Megazoids-Hut/PicoPocket/images/1.jpg

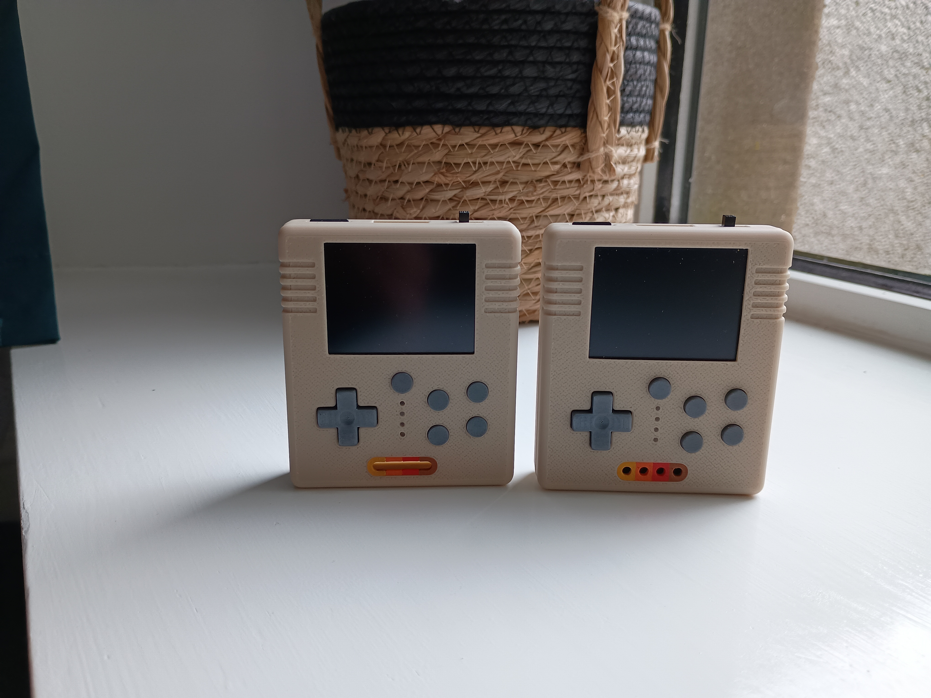
images/1.jpg
