Megazoids-Hut/PicoPocket/images/2.jpg

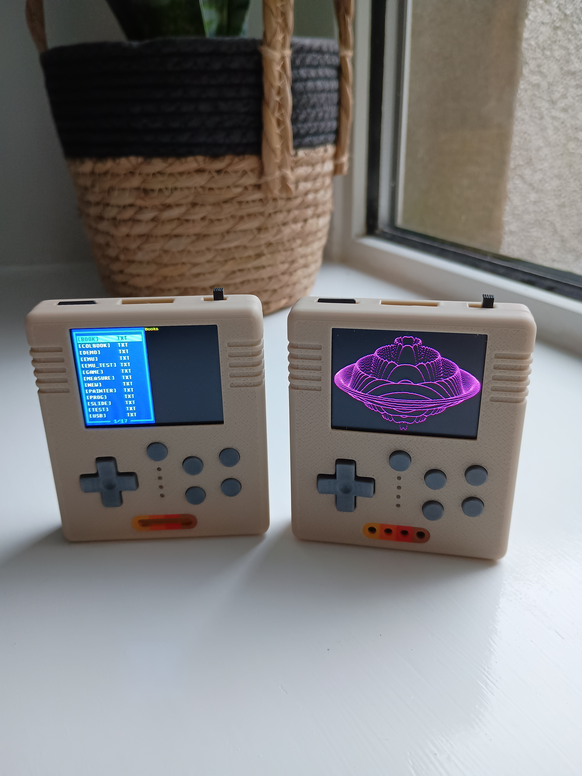
images/2.jpg
