Megazoids-Hut/PicoPocket/images/3.jpg

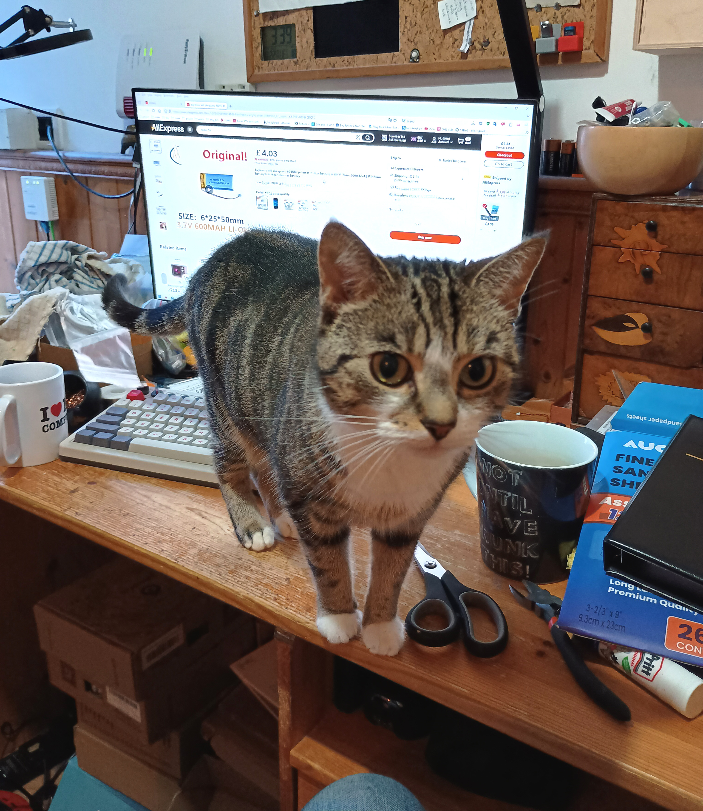
images/3.jpg
