Megazoids-Hut/PicoPocket/images/4.jpg

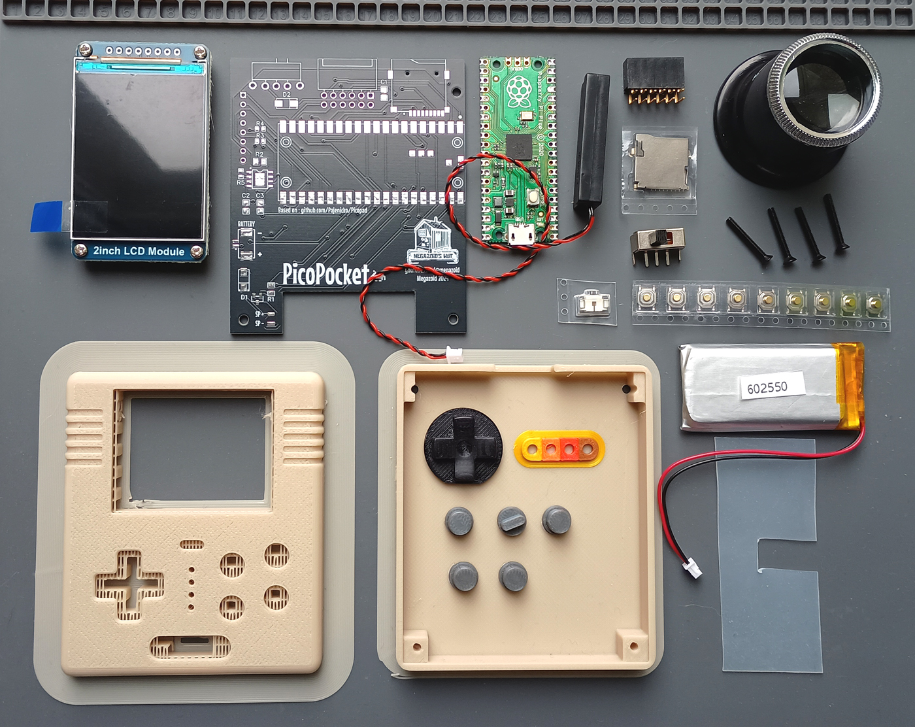
images/4.jpg
