Megazoids-Hut/PicoPocket/images/5.jpg

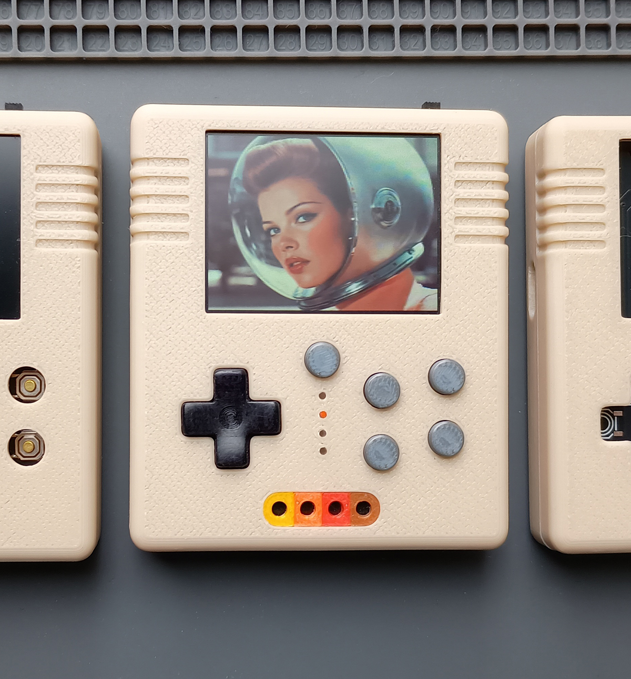
images/5.jpg
