Megazoids-Hut/PicoPocket/images/9.jpg

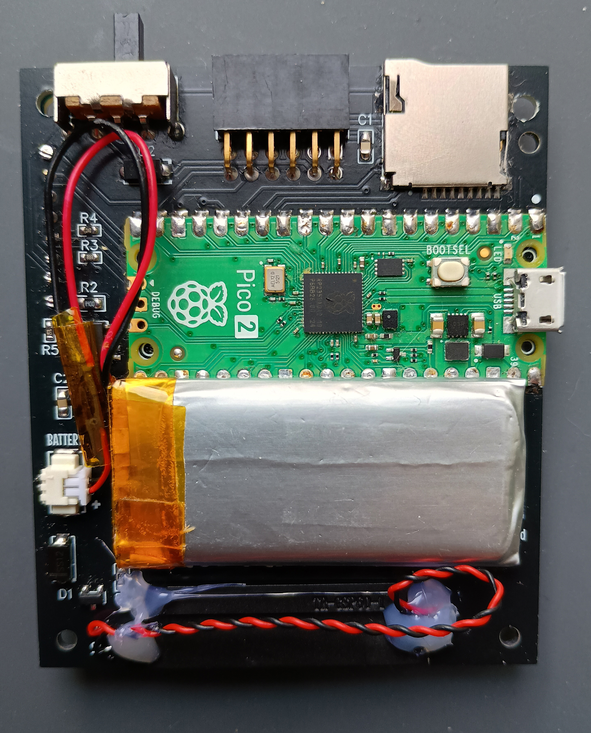
images/9.jpg
