Megazoids-Hut/PicoPocket/images/10.jpg

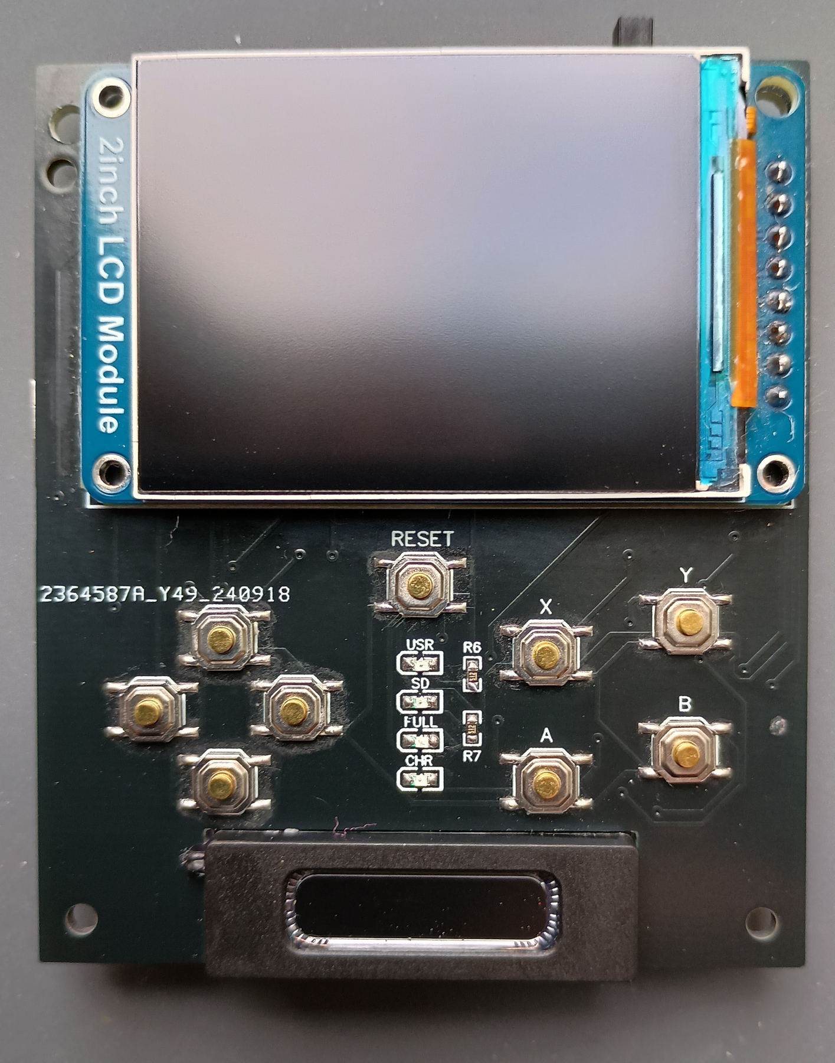
images/10.jpg
