Megazoids-Hut/PicoPocket/images/11.jpg

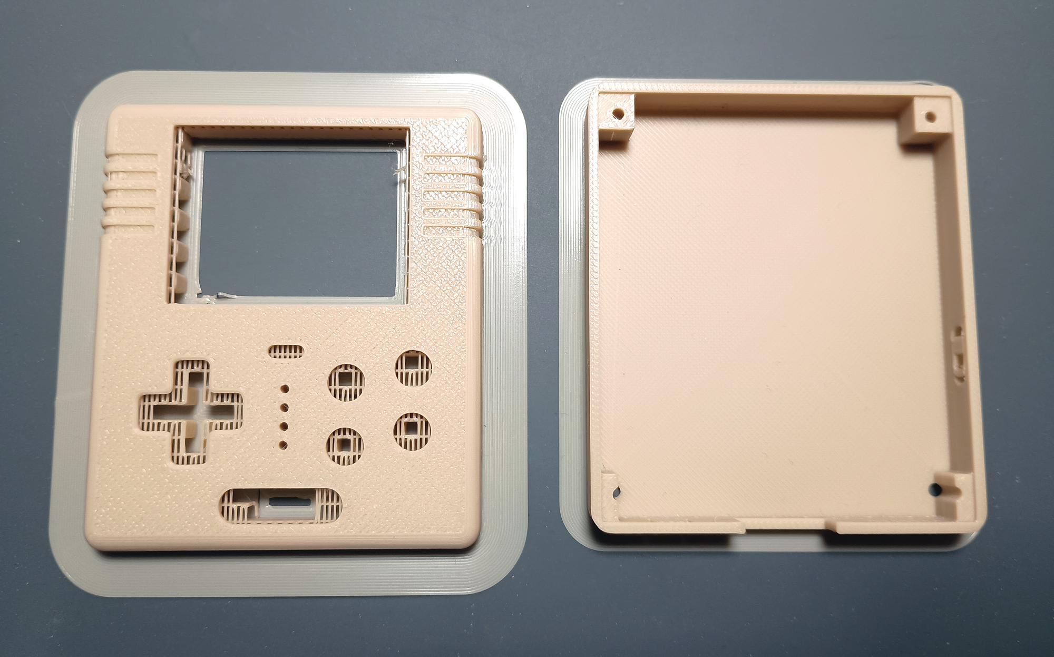
images/11.jpg
