Megazoids-Hut/PicoPocket/images/12.jpg

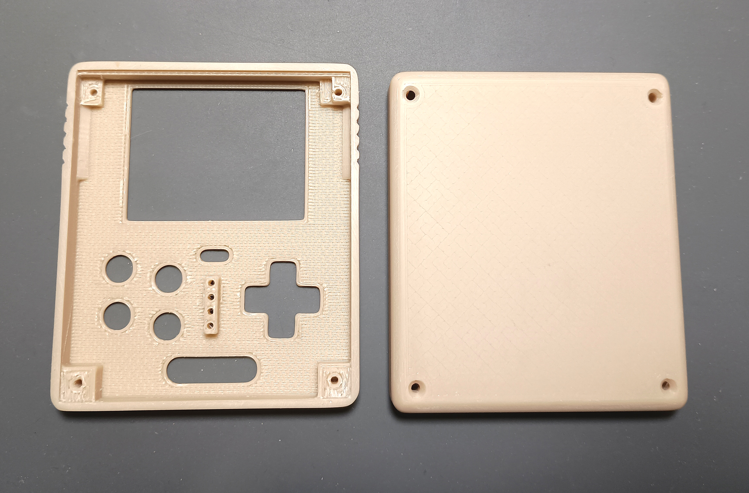
images/12.jpg
