Megazoids-Hut/PicoPocket/images/13.jpg

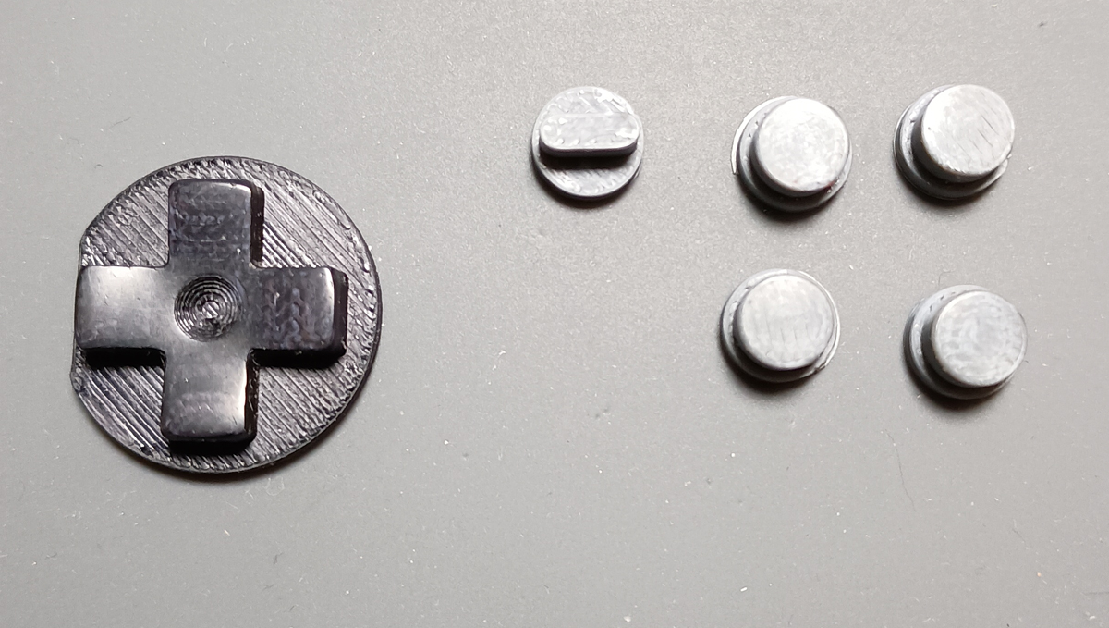
images/13.jpg
