Megazoids-Hut/PicoPocket/images/14.jpg

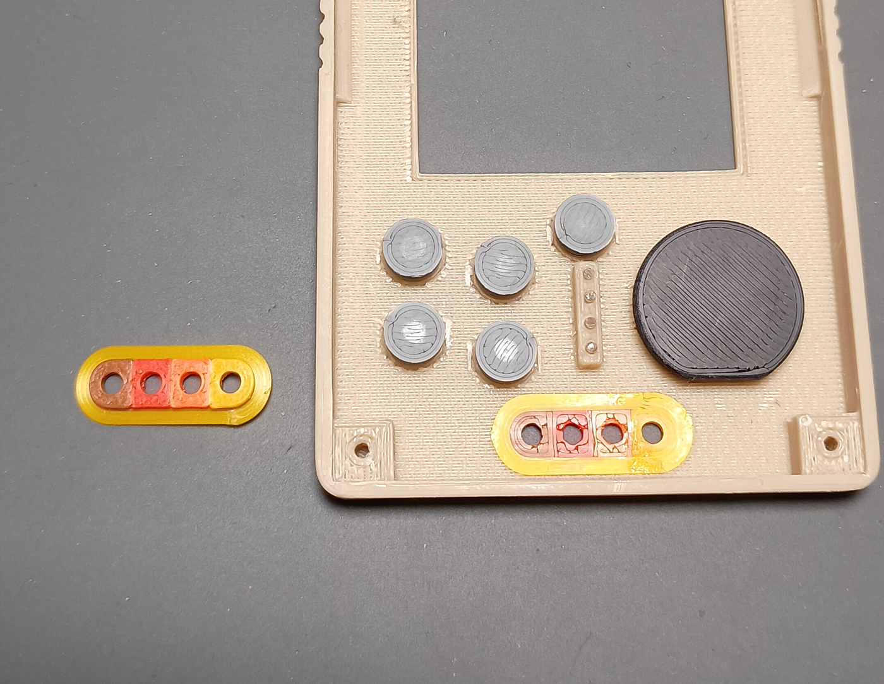
images/14.jpg
