Megazoids-Hut/PicoPocket/images/15.jpg

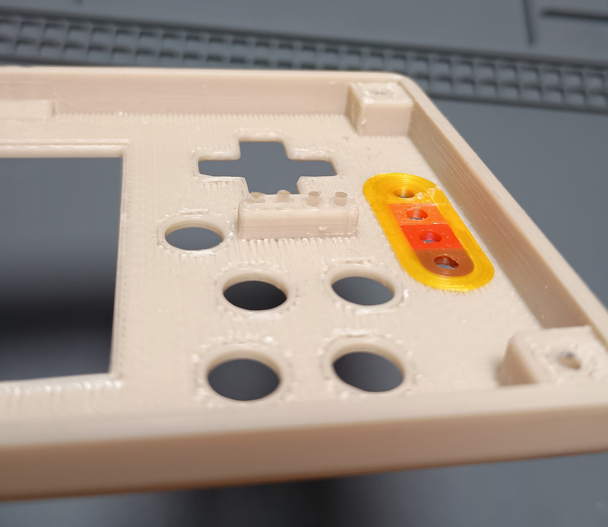
images/15.jpg
