Megazoids-Hut/PicoPocket/images/16.jpg

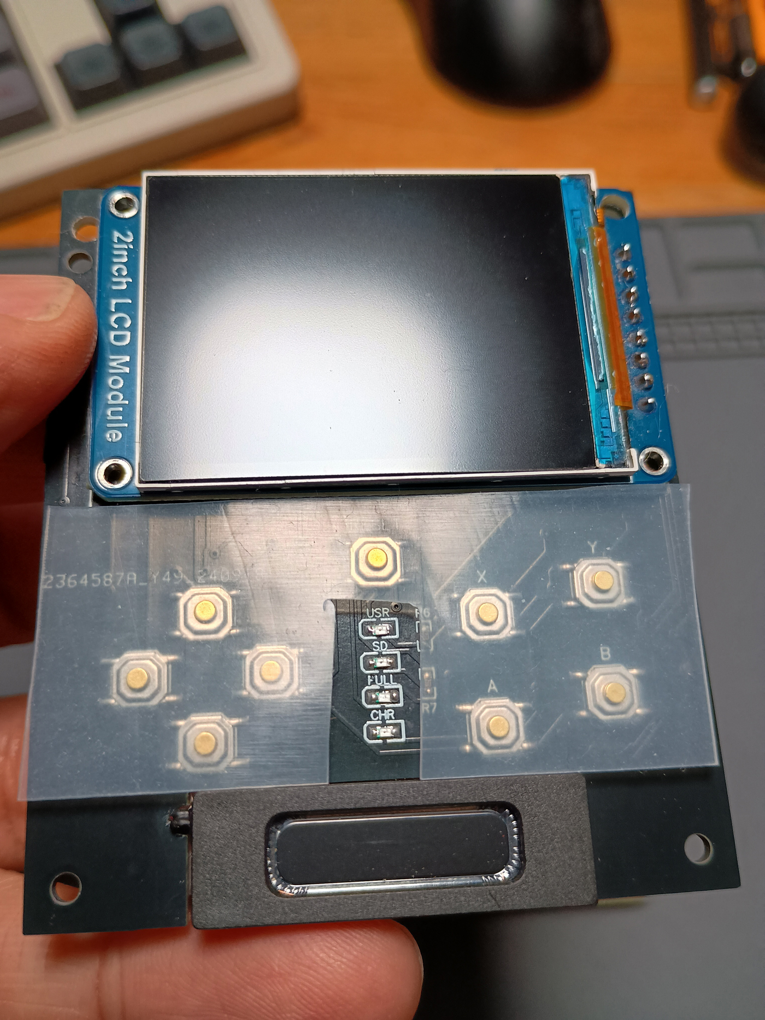
images/16.jpg
