Megazoids-Hut/PicoPocket/images/17.jpg

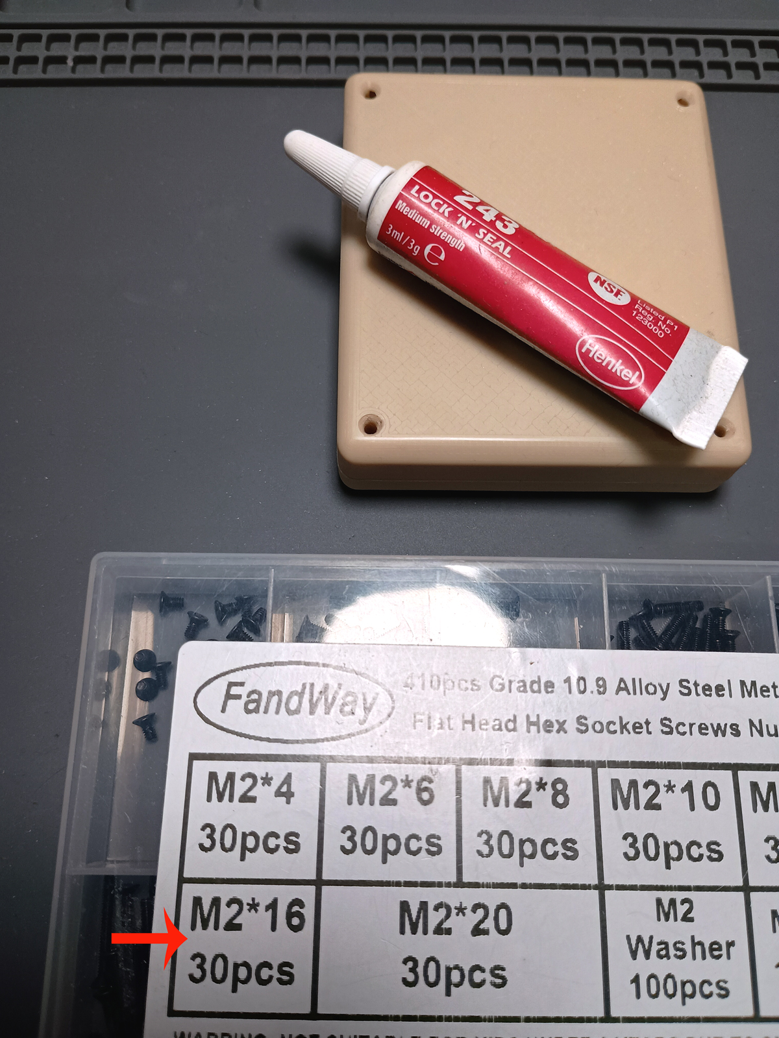
images/17.jpg
