Megazoids-Hut/PicoPocket/images/18.jpg

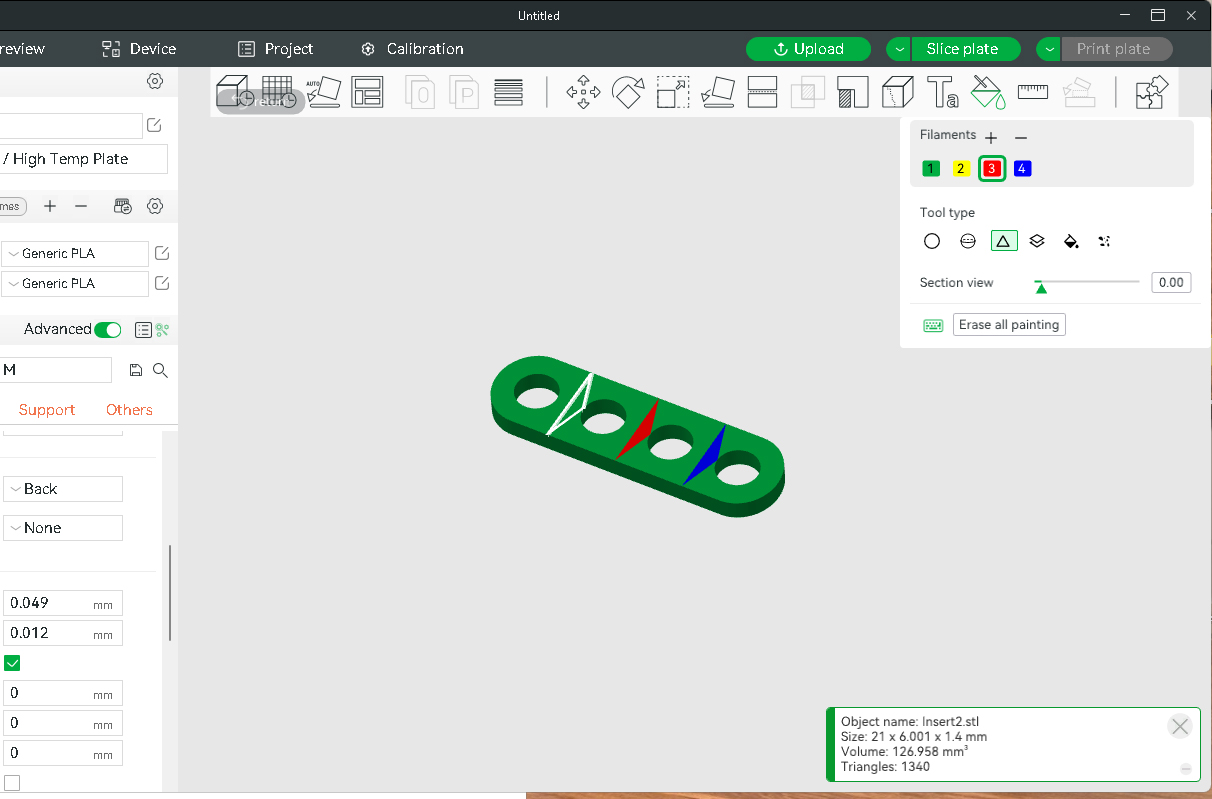
images/18.jpg
